komalkaurr/Group_3_Winter-2021/Interfacing touch screen display/Interfacing of touch screen display with BB-WI.pptx

## IOT Based Smart Restaurant Menu Using Beaglebone Black Wireless Task Interfacing Touch Screen Display with BB-WI

Submitted to:
Prof. Mike Aleshams
Submitted by:
Ramandeep Kaur
Group 3

## Block Diagram (Transmitter Side)

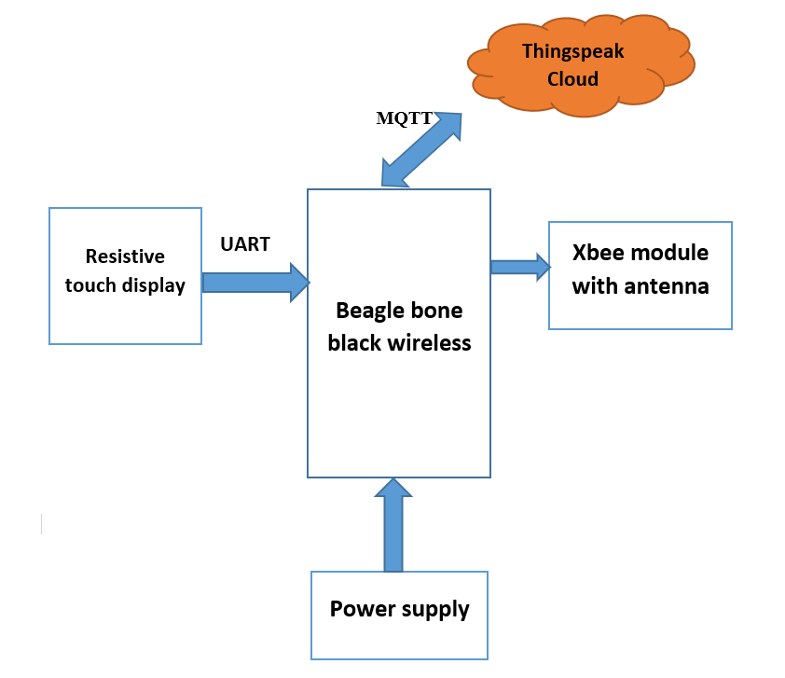
[picture p190: figure]

## Function of Touch Screen Display

- Through touch screen Display, customer can order food items.

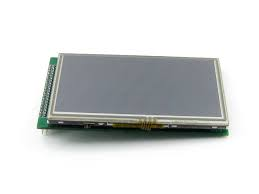
[picture p191: figure]

## Beaglebone Black Wireless

- Based on the extremely successful open-source BeagleBone Black hardware design, BeagleBone Black Wireless is a high-expansion, maker-focused, community-supported open hardware computer created by the BeagleBoard.org Foundation.

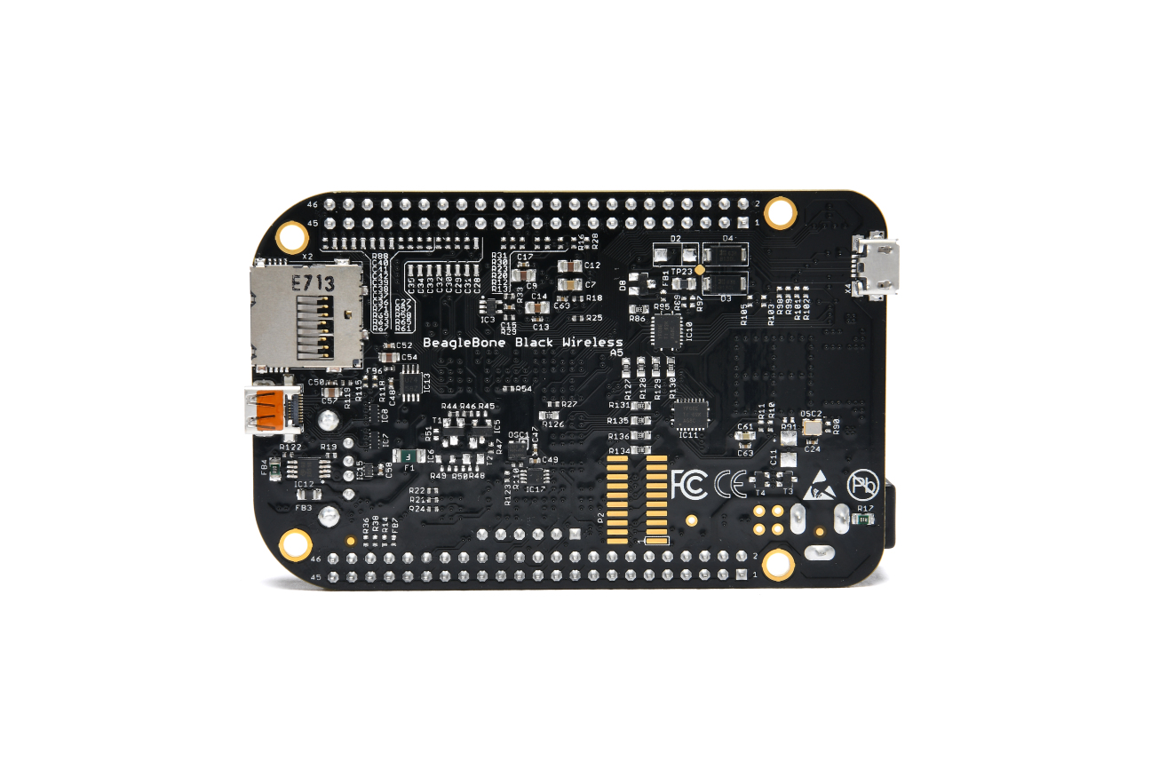
[picture p192: figure]

## Specifications of BB-WI

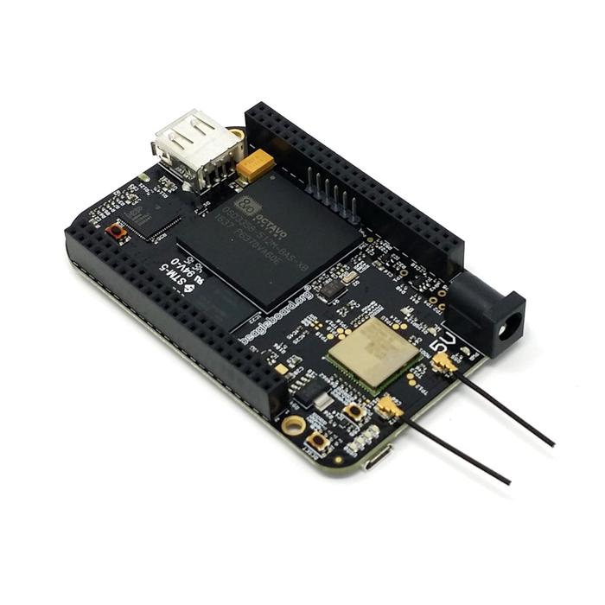
[picture p193: figure]

- 512MB DDR3 RAM
- 4GB 8-bit eMMC on-board flash storage
- 3D graphics accelerator
- NEON floating-point accelerator
- 2x PRU 32-bit microcontroller
- Processor: Octavo systems OSD3358 1GHz ARM Cortex-A8

## Pin Diagram of Beaglebone Black Wireless


## The 4.3’’ Resistive Touch LCD

Nextion NX4827T043 4.3 Inch HMI Intelligent Smart USART UART Serial Touch TFT LCD Screen Module Display Panel:
- Nextion is a Seamless Human Machine Interface (HMI) solution that provides a control and visualization interface between a human and a process, machine, application or appliance. It is the best solution to replace the traditional LCD and LED Nixie tube. Nextion includes hardware part (a series of TFT boards) and software part (the Nextion Editor).

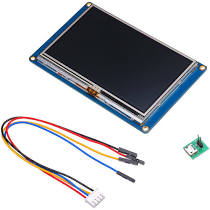
[picture p194: figure]

## The 4.3’’ Resistive Touch LCD

- The Nextion TFT board uses only one serial port to communicate. It lets you avoid the hassle of wiring. We notice that most engineers spend much time in application development but get unsatisfactory results. In this situation, Nextion editor has mass components such as button, text, progress bar, slider, instrument panel etc. to enrich your interface design.

## Features

- 480 x 272 Resolution
- RGB 65K true to life colours
- TFT Screen with integrated 4-wire Resistive Touch Panel
- Easy 4 pin interface to any TTL Serial Host
- 16M Flash memory for User Application Code and Data
- On board micro-SD card for firmware upgrade
- Visual Area:95.04mm(L)×53.86mm(W)
- Adjustable Brightness:0~230 nit, the interval of adjustment is 1%
- 5V250mA power consumption

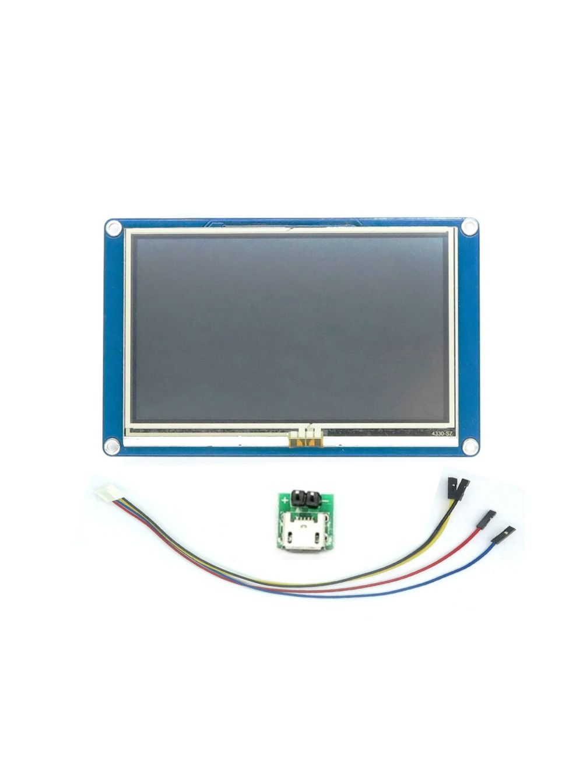
[picture p195: figure]

## Basic elements of LCD touch screen

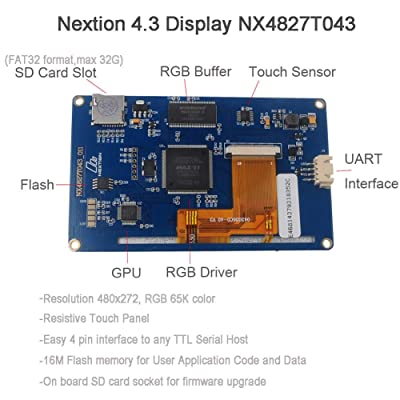
[picture p196: figure]

## Pins of Touch screen display

- Following 4 pins are needed for UART interfacing
1. +5v
2.Tx
3. Rx
4.GND

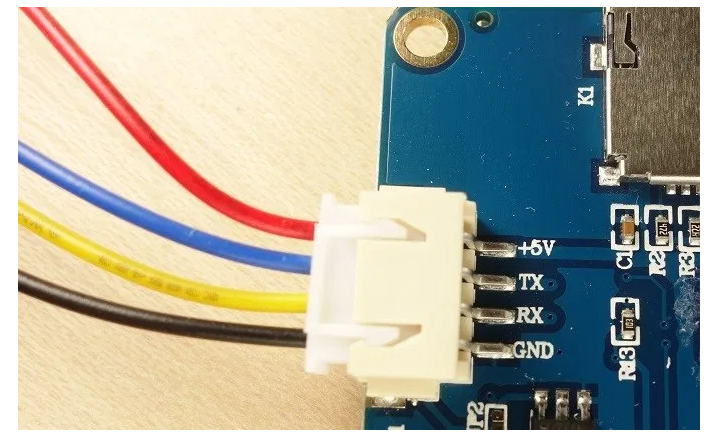
[picture p197: figure]

## Interfacing Touch Screen Display with BB-WI

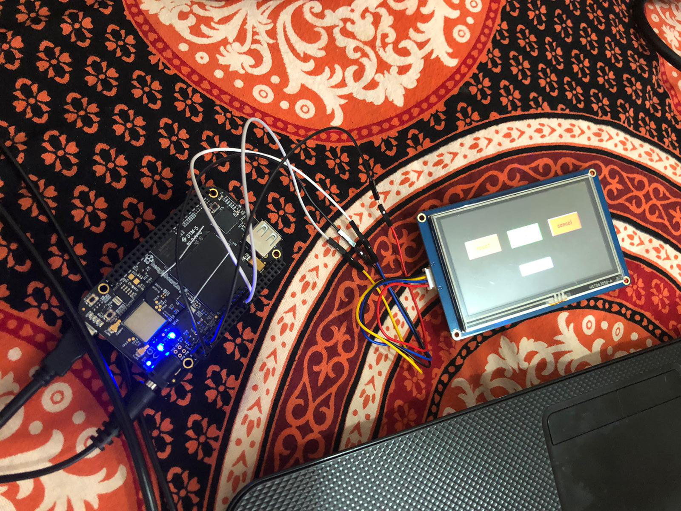
[picture p198: figure]

## Slide 13

Beaglebone Black Wireless | Touch Screen Display
P9_6(VDD_5V) | +5V
P9_1(DGND) | GND
P9_26(UART1_RxD) | Tx
P9_24(UART1_TXD) | Rx

## Nextion Editor

- Nextion is a Human Machine Interface （HMI） solution combining an onboard processor and memory touch display with Nextion Editor software for HMI GUI project development.
- We need Nextion editor for creating GUI on touch screen display.

## Nextion Editor

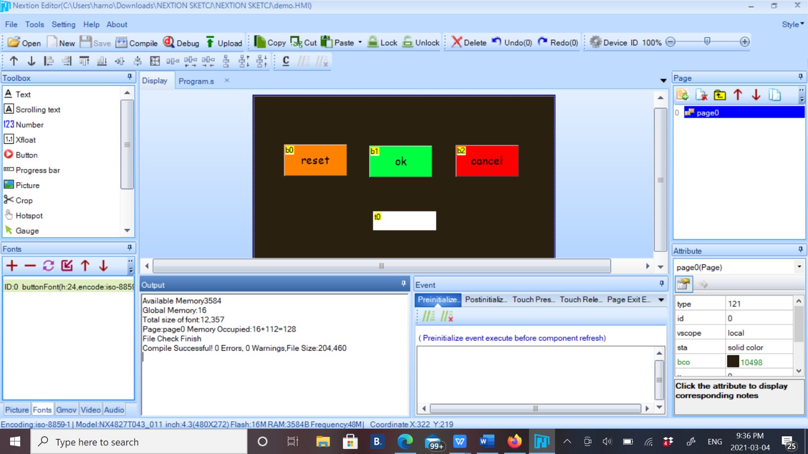
[picture p199: figure]

## Interfacing communication protocol:UART

- A universal asynchronous receiver-transmitter (UART) is a computer hardware device for asynchronous serial communication (https://en.wikipedia.org/wiki/Asynchronous_serial_communication) in which the data format and transmission speeds are configurable.
- It sends data bits one by one, from the least significant to the most significant, framed by start and stop bits so that precise timing is handled by the communication channel.


## Interfacing communication protocol:UART

- Beaglebone Black Wireless have 4.5 serial UARTs.
- For interfacing with touch screen display, we can use either of UART1, UART2, UART4.
- We cannot use UART3 for interfacing with touch screen display, because UART3 has only transmit pin.


## SSH to Beaglebone Black Wireless

- Type this command in terminal and make ssh connection to BB-WI
ssh Debian@192.168.7.2
- After this, put default password “temppwd”

## SSH to Beaglebone Black Wireless


## Python code for Touch screen Display

- Firstly, create a new file in BBB terminal through following command:
Sudo nano <file name>
- For Python file, use .py extension with file name

## Python code for Touch screen Display

## Python code for Touch screen Display

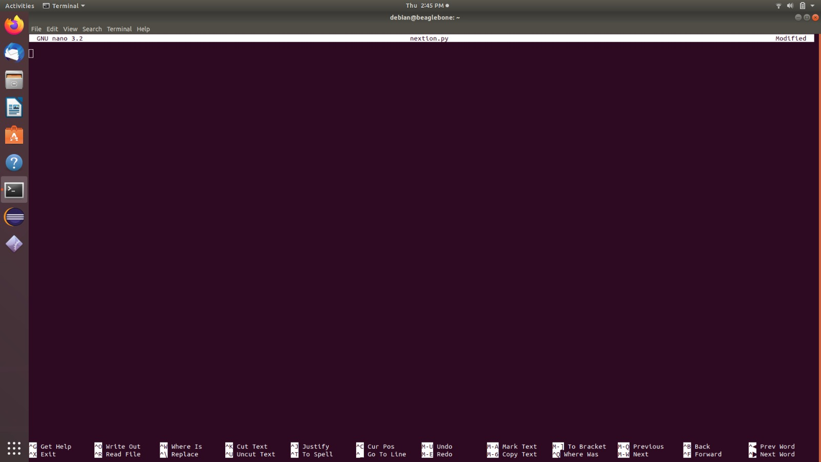
[picture p200: figure]

## Python code for Touch screen Display

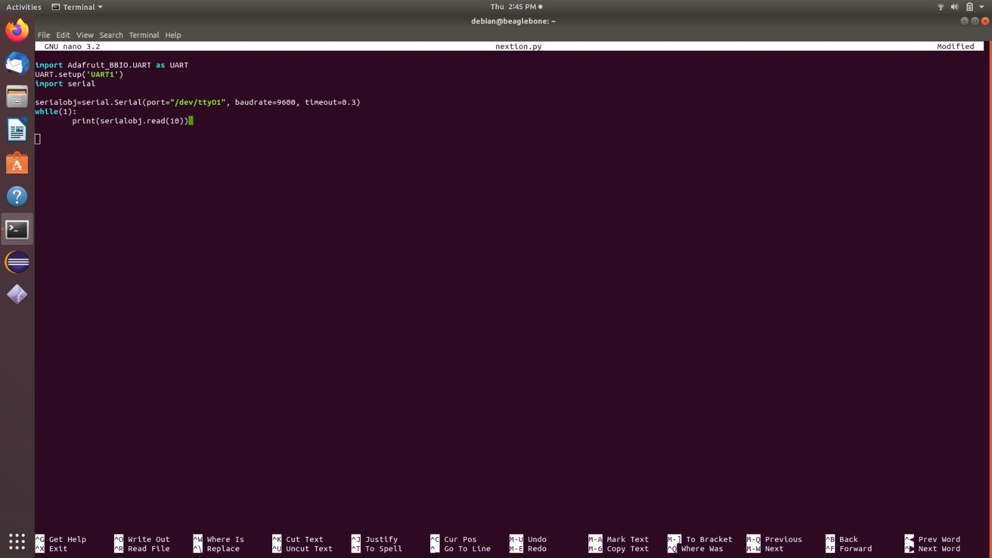
[picture p201: figure]

## Python code :

- import Adafruit_BBIO.UART as UART
UART.setup("UART1")
#These lines used for enabling the UART and importing Adafruit_BBIO library.

- Import serial
# For importing serial library, which we need for transmitting and receiving data,

serialobj= serial.Serial(port = "/dev/ttyO1", baudrate=9600, timeout=0.3)
While(1):
print(serialobj.read(10))

## Python code:

- serialobj= serial.Serial(port = "/dev/ttyO1", baudrate=9600, timeout=0.3)
While(1):
- port = "/dev/ttyO1“
#ttyo1 represents UART1

- print(serialobj.read(10))
#For printing data on Beaglebone Black Wireless

## Download Library

- The Adafruit IO Python library will export the UART device tree overlays as a convenience.
import Adafruit_BBIO.UART as UART
UART.setup("UART1")

## Download Library

- To use UART with python, we can use pyserial module.
- We can install it using pip with following command:
pip3 install pyserial
- pip is package installer for python.

## Download Library

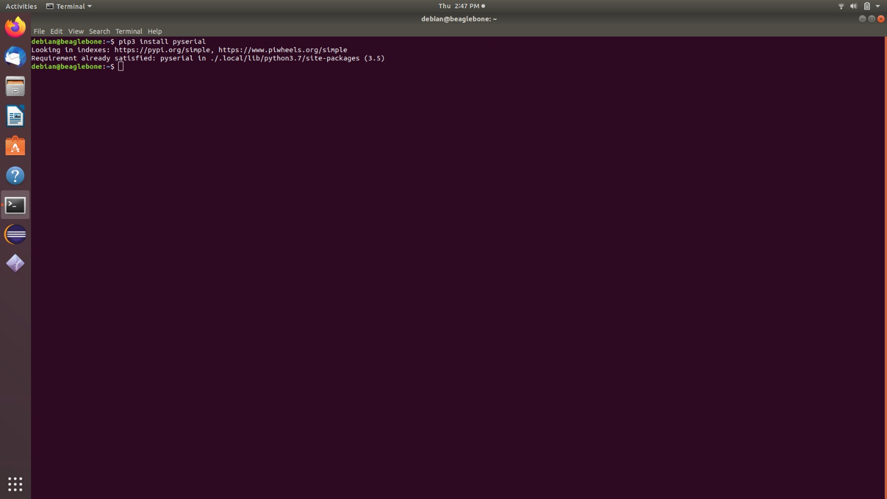
[picture p202: figure]

## Run the Program

- We can run the python code with the help of following command:
python3 <file name>

## Output:

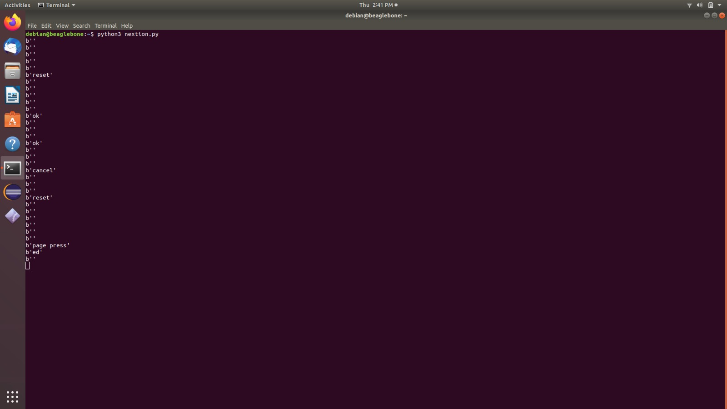
[picture p203: figure]

## References:

- For installing Library:
https://learn.adafruit.com/setting-up-io-python-library-on-beaglebone-black/uart
- Specifications of touch screen display:
https://pl.aliexpress.com/item/32874330873.html
- Nextion Ediotr:
https://www.youtube.com/watch?v=qx-aFB3-7SA

## References:

- Interfacing of BB-WI with touch screen display:
https://www.14core.com/working-with-nextion-hmi-gui-tft-touch-display/
- Specifications of BB-WI:
https://beagleboard.org/black-wireless
